EslaFunk/TigerVent/TigerVent/src/ventsettings.h

#ifndef ventsettings_h
#define ventsettings_h

enum AlarmType {NoAlarm, HighPressureAlarm, LowPressureAlarm};
enum OperatingMode {VolumeControl, AssistControl, SynchronizedIntermittentMandatoryVentilation}; 


typedef struct  {

  // Current slave mode.
  char mode;

  // Ventilation settings.
  int tidal_volume;
  int respiration_rate;
  int inhale;
  int exhale;
  int hold_seconds;
  int hold_decimals;

  // Time between trajectory points.
  int delta_time;

  // Current ventilation time.
  int hours;
  int minute;
  int seconds;

  // Boolean to indicate to send settings.
  bool send;

  AlarmType alarm_type;

  OperatingMode operatingMode;

} VentSettings;

typedef struct {

  // Limits for ventilation settings.
  int min_tidal_volume = 300;
  int max_tidal_volume = 700;
  int delta_tidal_volume = 50;

  int min_respiration_rate = 10;
  int max_respiration_rate = 30;
  int delta_respiration_rate = 1;

  int min_exhale = 1;
  int max_exhale = 5;
  int delta_exhale = 1;

} VentLimits;

#endif
